LaurentFrx/camera-RPi5-comptage/hardware/camera-arm/renders/05_pose_plongee.png

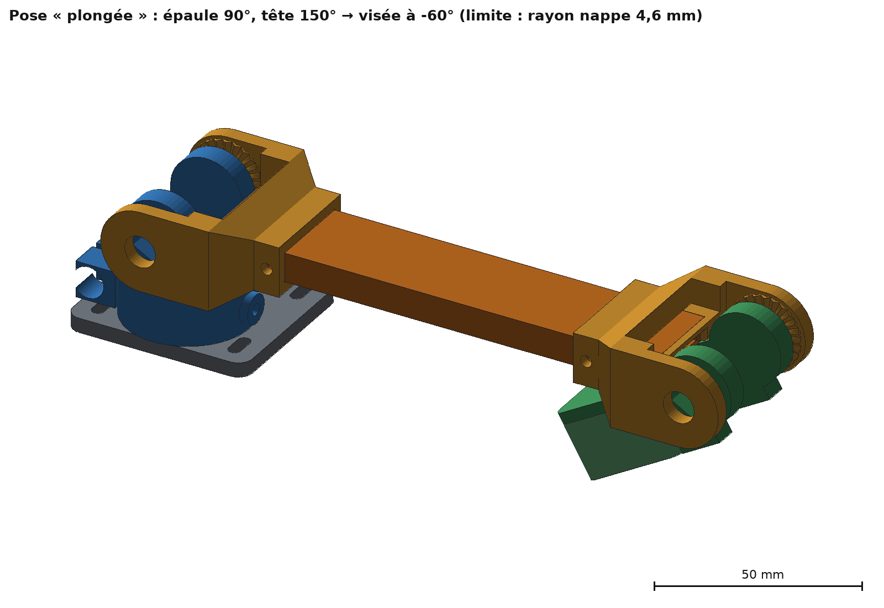
hardware/camera-arm/renders/05_pose_plongee.png
