LaurentFrx/camera-RPi5-comptage/hardware/camera-arm/renders/20_piece_01b_cavalier_adaptateur.png

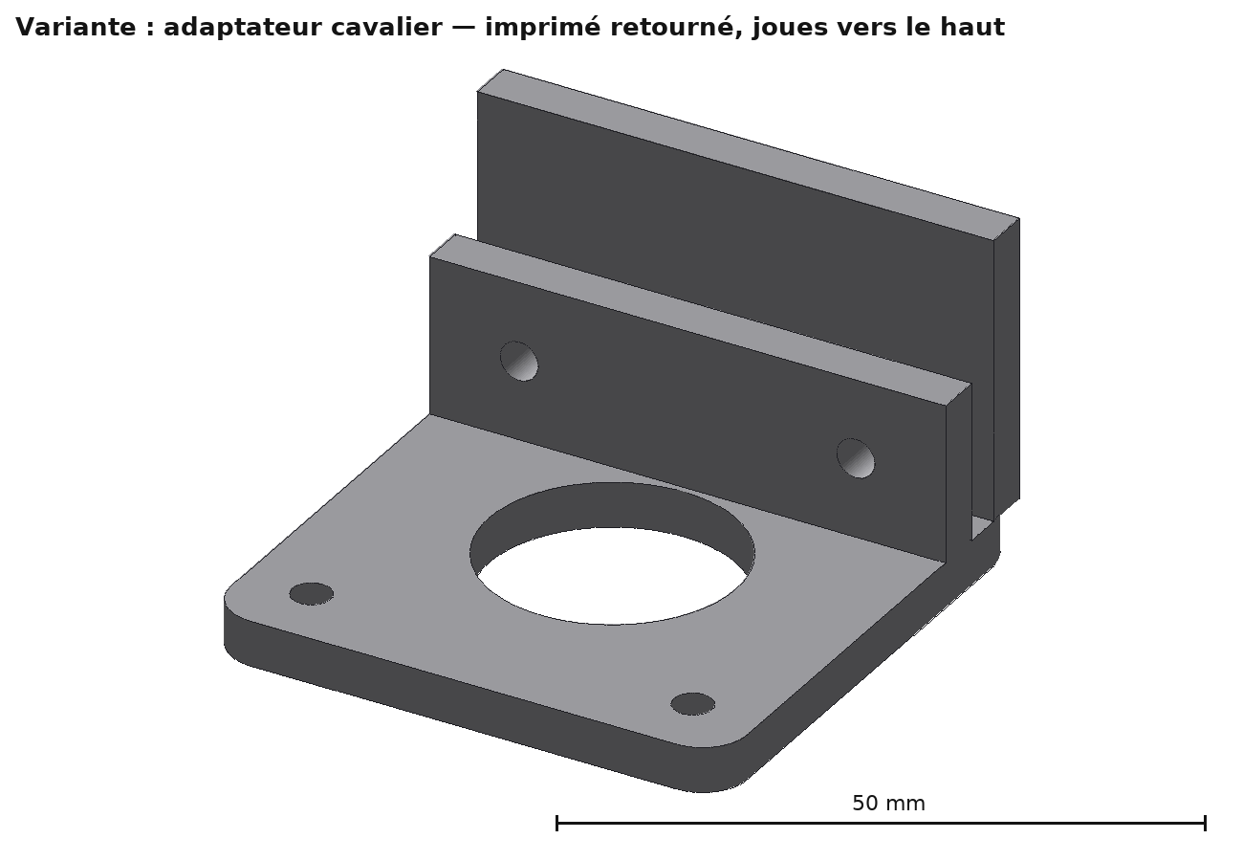
hardware/camera-arm/renders/20_piece_01b_cavalier_adaptateur.png
