LaurentFrx/camera-RPi5-comptage/hardware/camera-arm/renders/20_piece_01c_gabarit_percage_couvercle.png

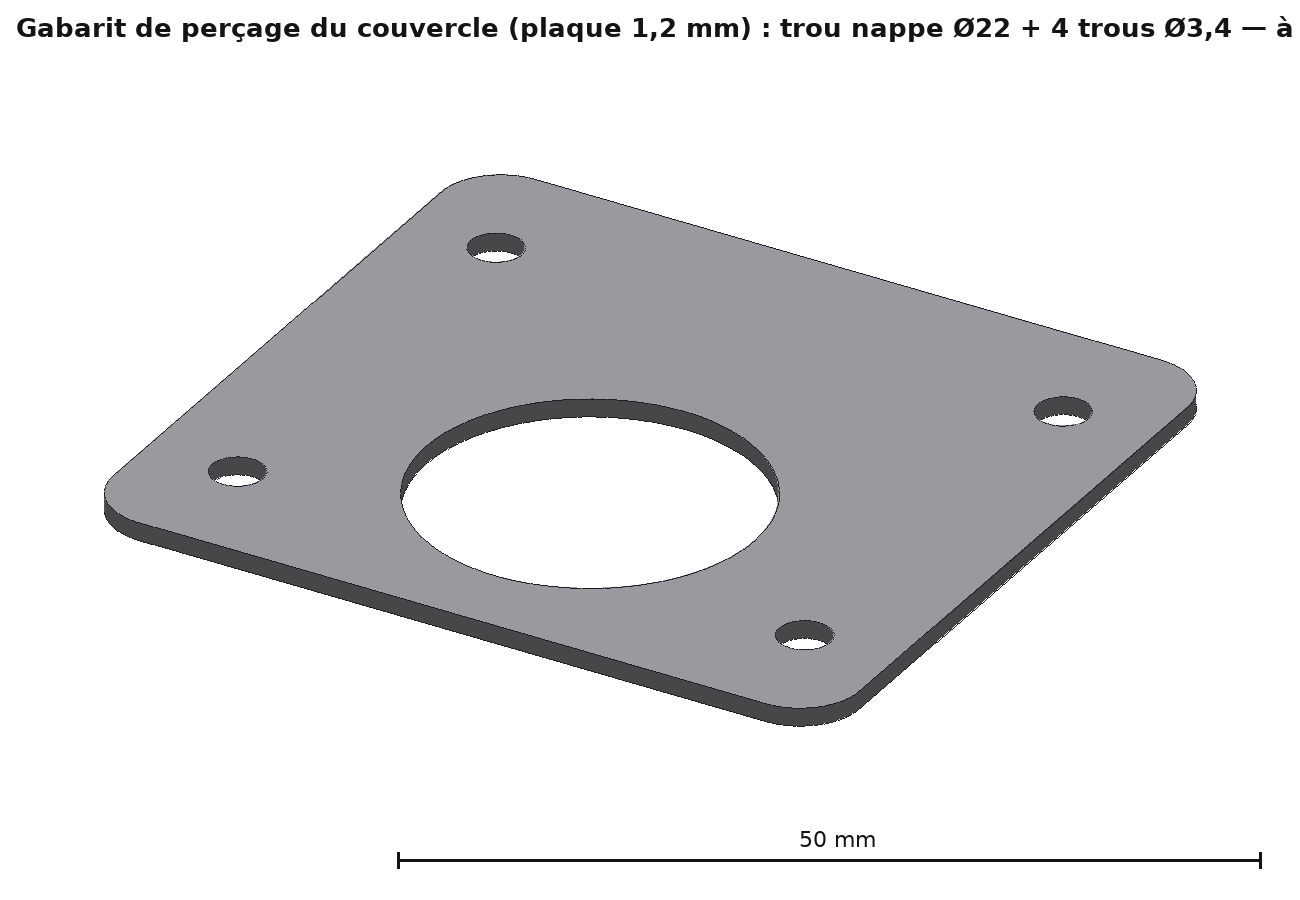
hardware/camera-arm/renders/20_piece_01c_gabarit_percage_couvercle.png
