LaurentFrx/camera-RPi5-comptage/hardware/camera-arm/renders/20_piece_04a_bras_corps_L150.png

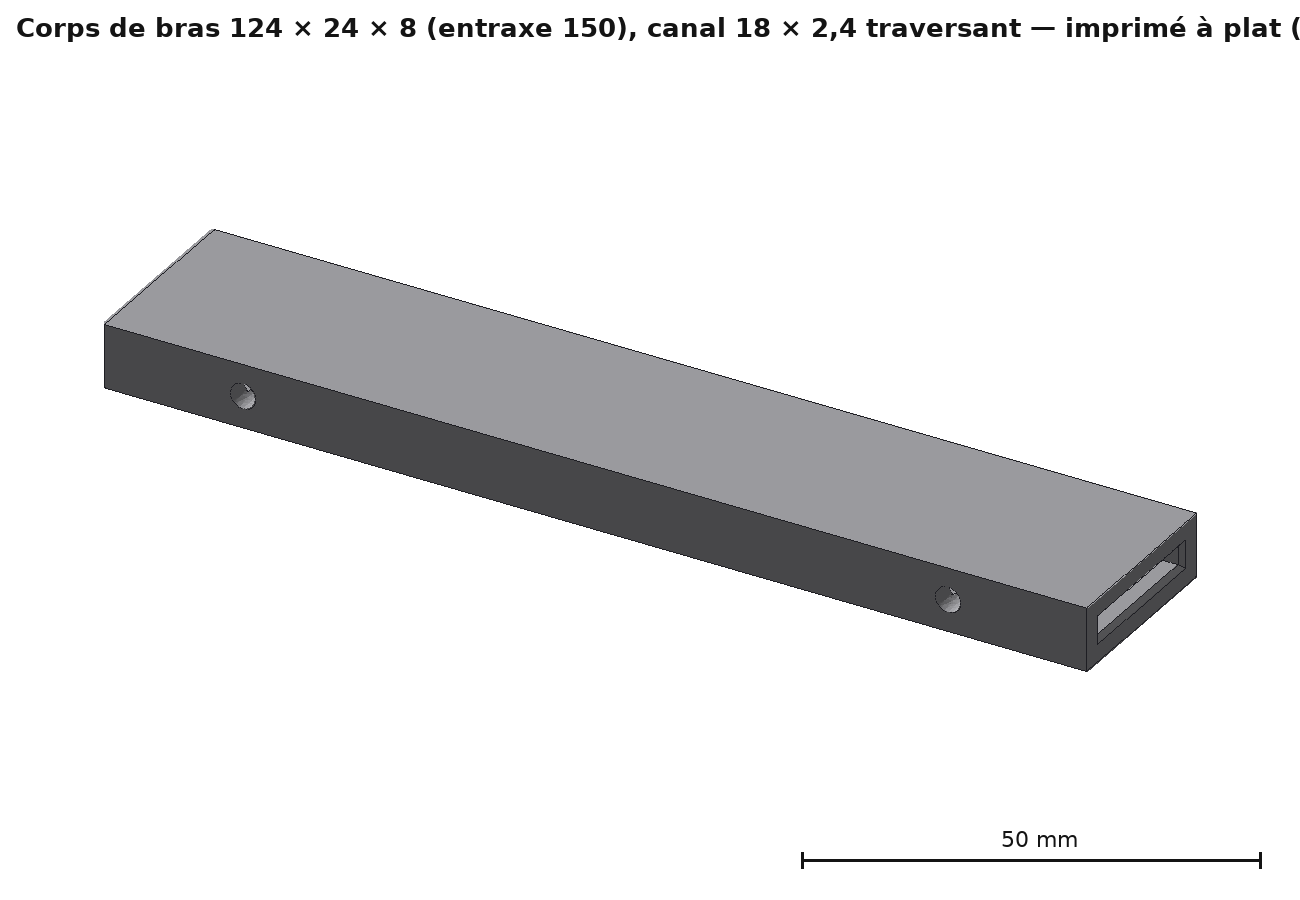
hardware/camera-arm/renders/20_piece_04a_bras_corps_L150.png
