LaurentFrx/camera-RPi5-comptage/hardware/camera-arm/renders/20_piece_04a_bras_corps_L170_alt.png

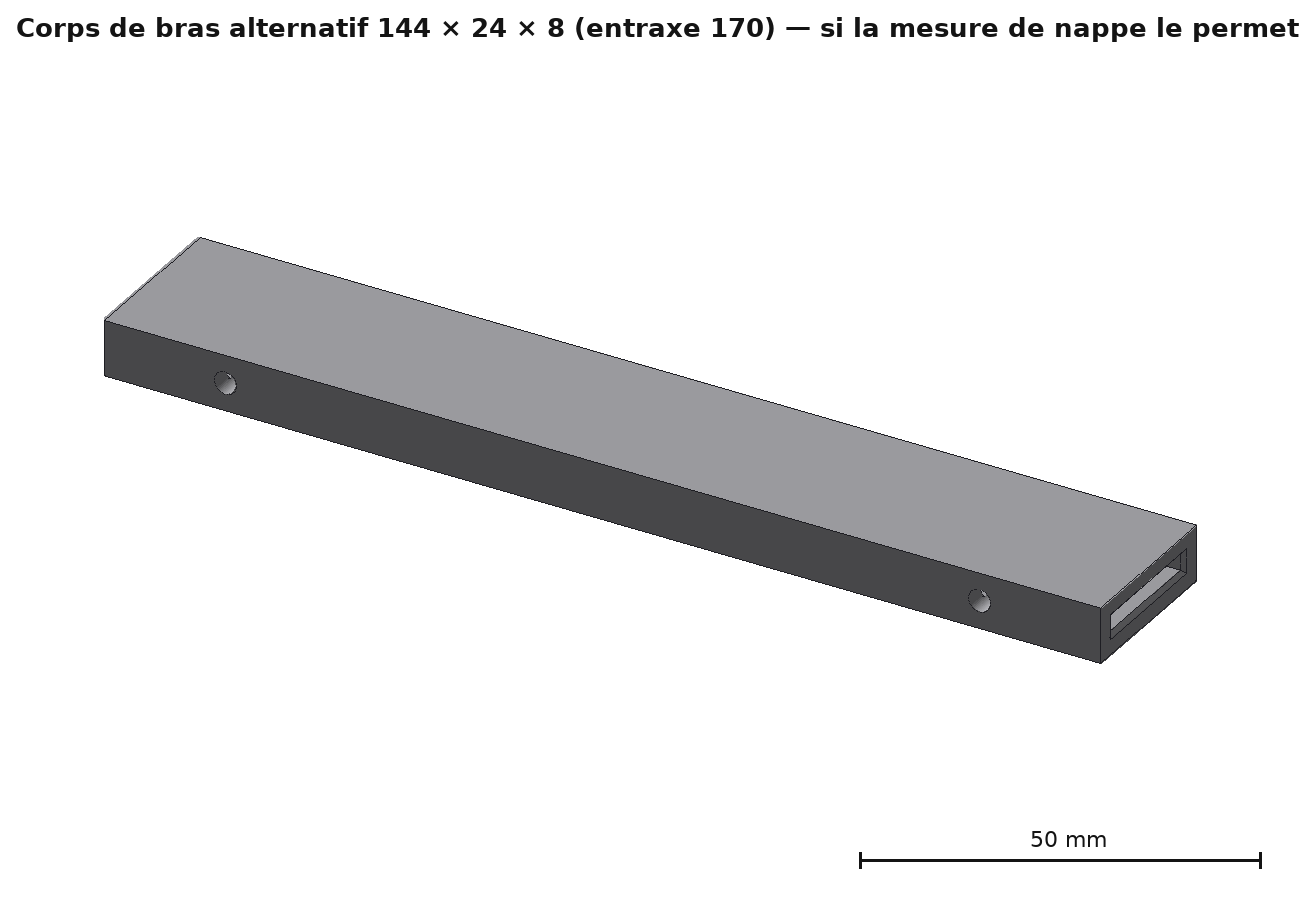
hardware/camera-arm/renders/20_piece_04a_bras_corps_L170_alt.png
