LaurentFrx/camera-RPi5-comptage/hardware/camera-arm/renders/20_piece_04c_goupille_x5.png

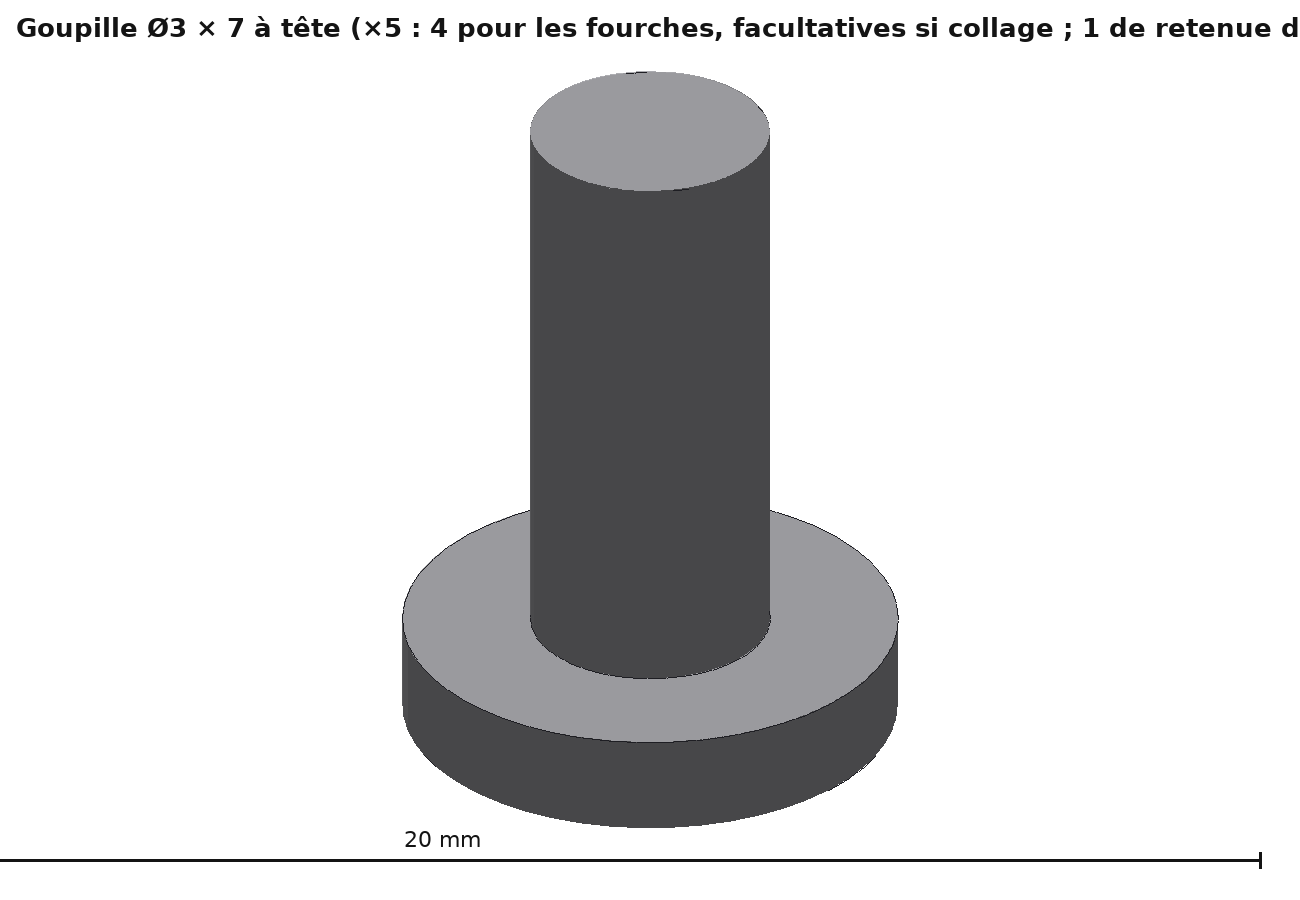
hardware/camera-arm/renders/20_piece_04c_goupille_x5.png
