LaurentFrx/camera-RPi5-comptage/hardware/camera-arm/renders/20_piece_06_tete_facade.png

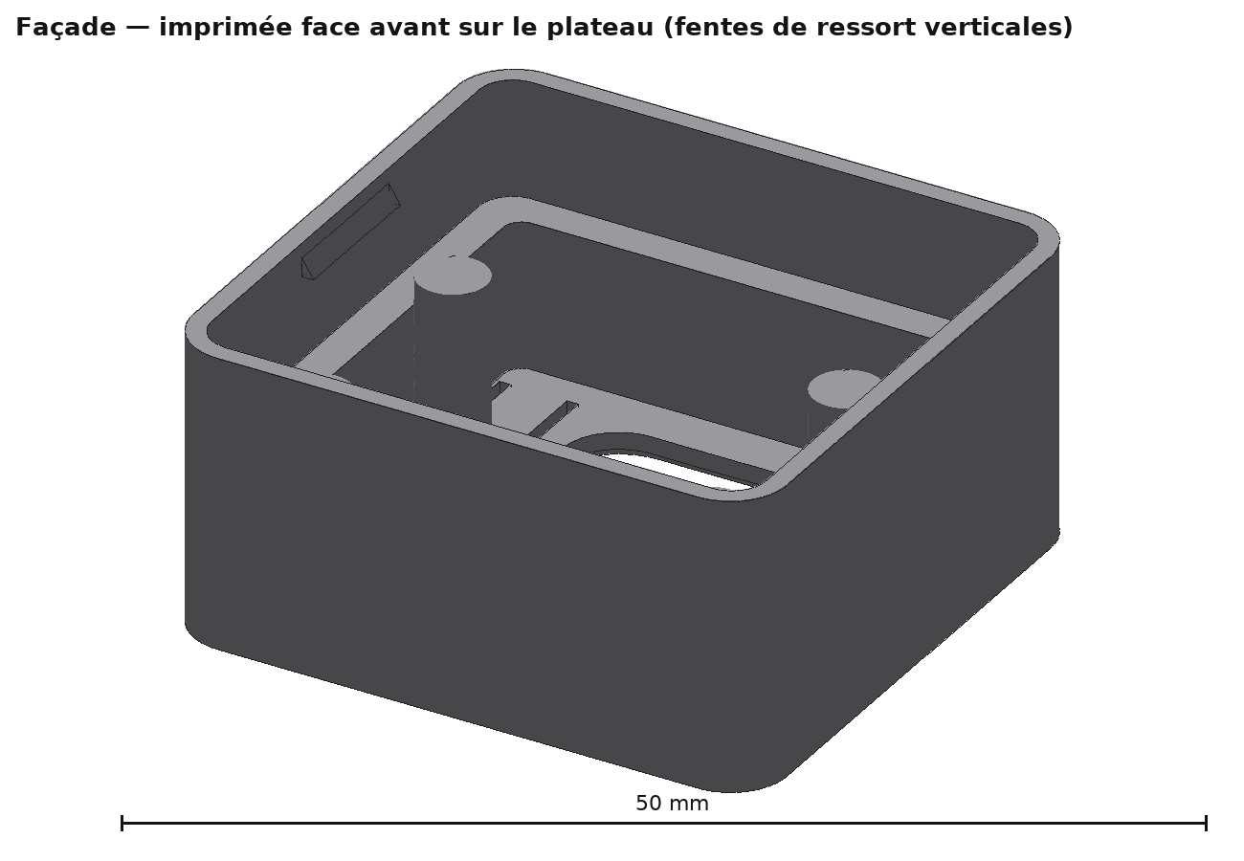
hardware/camera-arm/renders/20_piece_06_tete_facade.png
