LaurentFrx/camera-RPi5-comptage/hardware/camera-arm/renders/20_piece_07_vis_M8_L11_x4.png

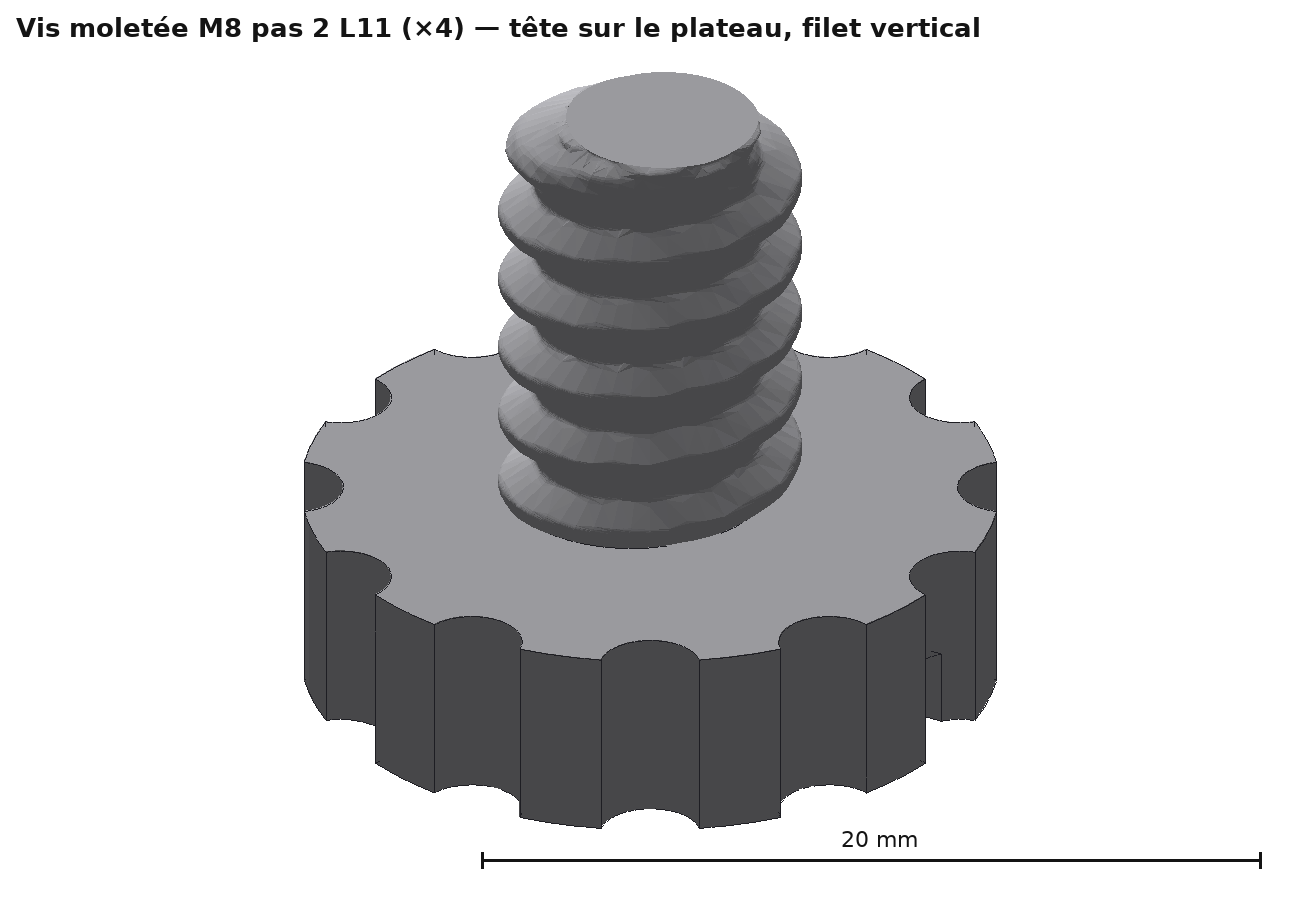
hardware/camera-arm/renders/20_piece_07_vis_M8_L11_x4.png
