LaurentFrx/camera-RPi5-comptage/hardware/camera-arm/renders/20_piece_09_ecrou_rosette_x4.png

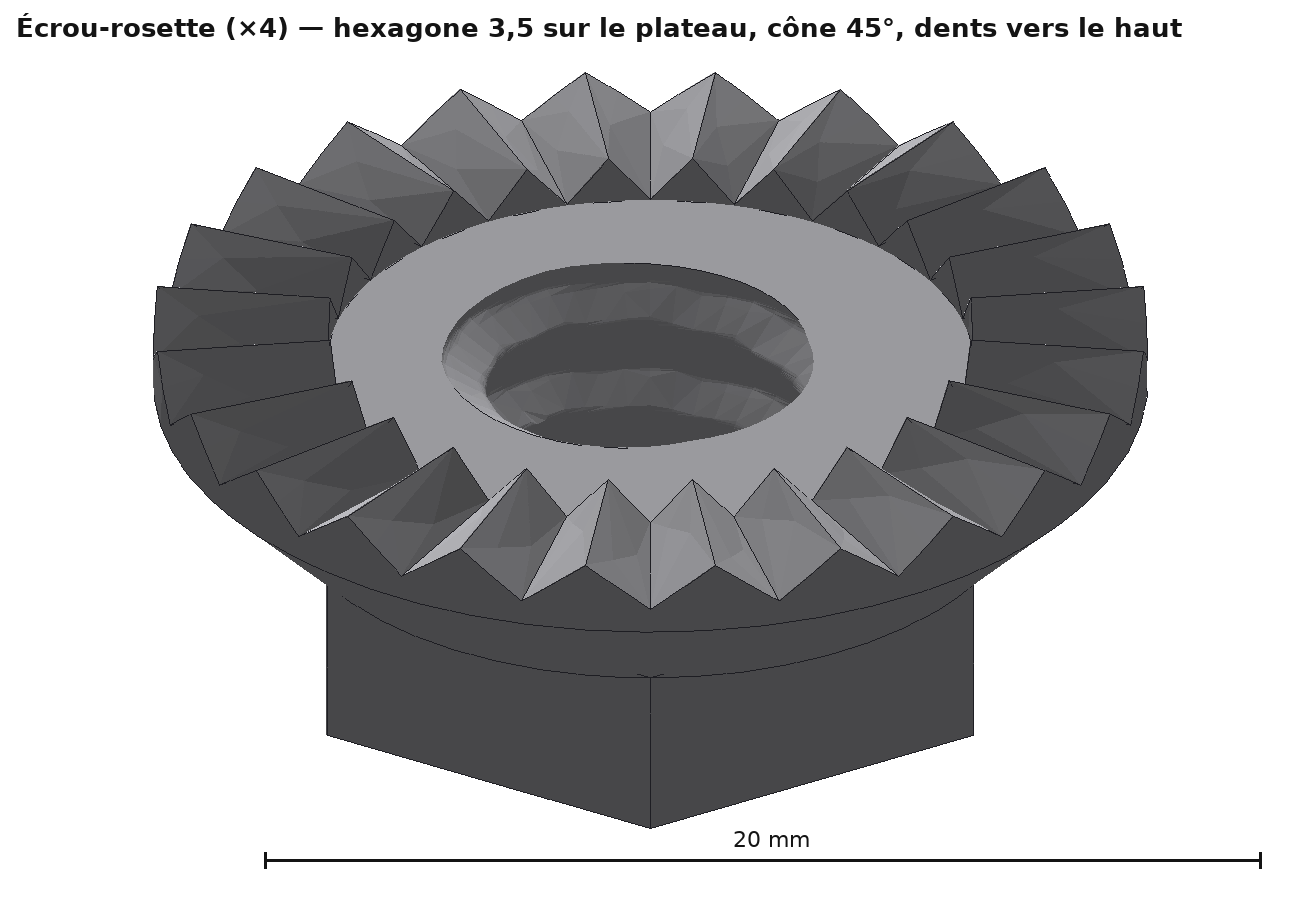
hardware/camera-arm/renders/20_piece_09_ecrou_rosette_x4.png
