LaurentFrx/camera-RPi5-comptage/hardware/camera-arm/renders/20_piece_10_ecrou_hex.png

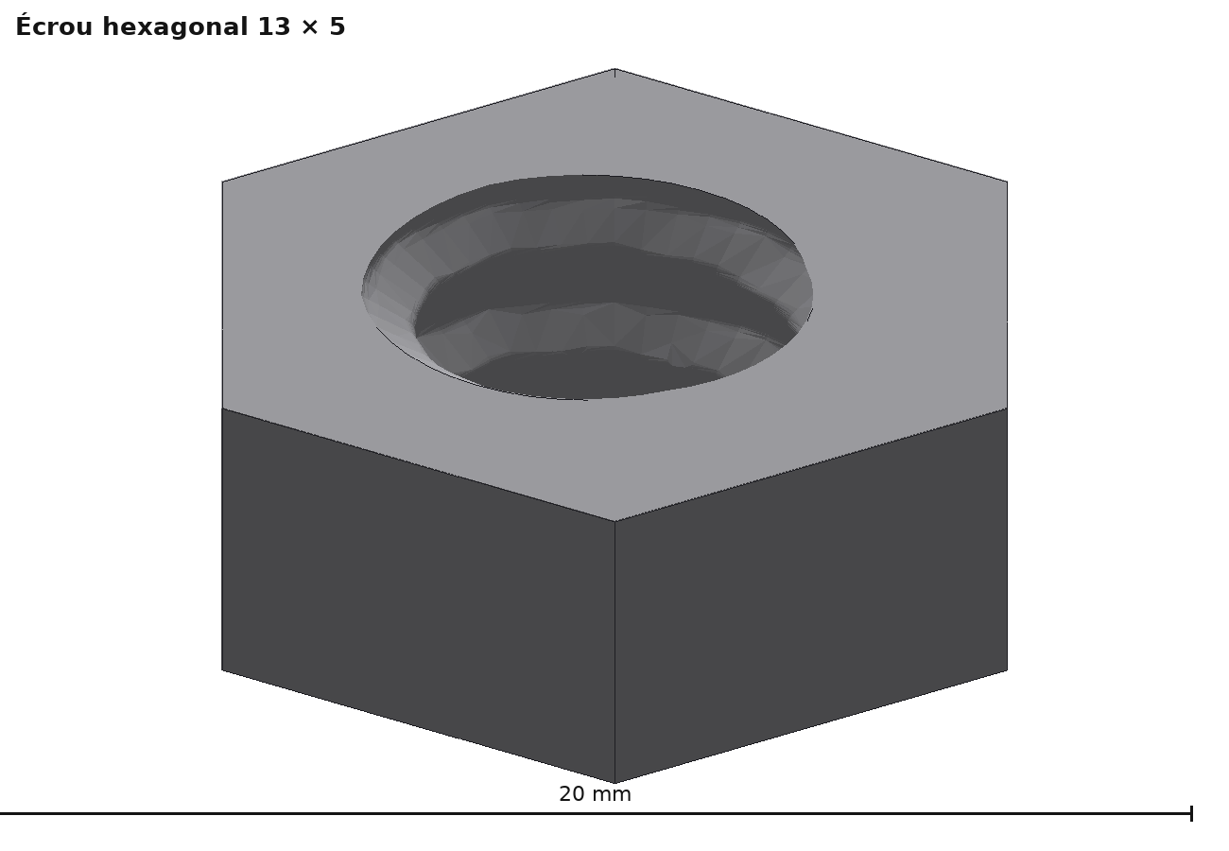
hardware/camera-arm/renders/20_piece_10_ecrou_hex.png
