LaurentFrx/camera-RPi5-comptage/hardware/camera-arm/export/step/10_ecrou_hex.step

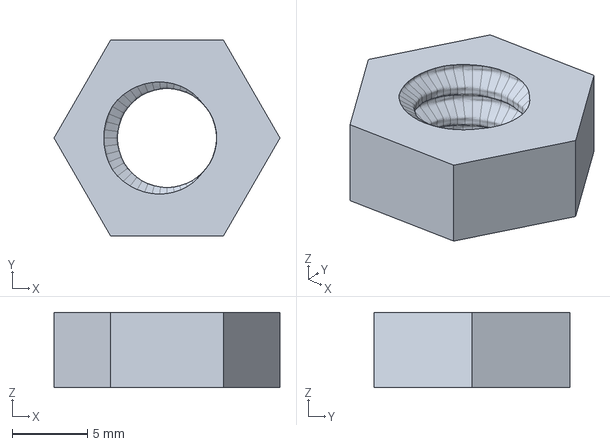
[picture p47: CAD file, 2026-10-01]
hardware/camera-arm/export/step/10_ecrou_hex.step
15.0 x 13.0 x 5.00 mm
