LaurentFrx/camera-RPi5-comptage/hardware/camera-arm/export/step/04a_bras_corps_L170_alt.step

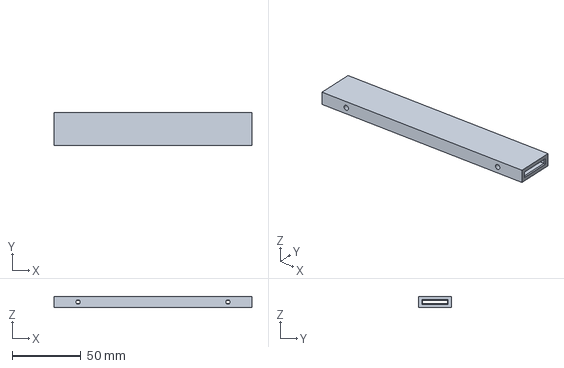
[picture p48: CAD file, 2026-10-01]
hardware/camera-arm/export/step/04a_bras_corps_L170_alt.step
144.0 x 24.0 x 8.00 mm
