LaurentFrx/camera-RPi5-comptage/hardware/camera-arm/export/step/04c_goupille_x5.step

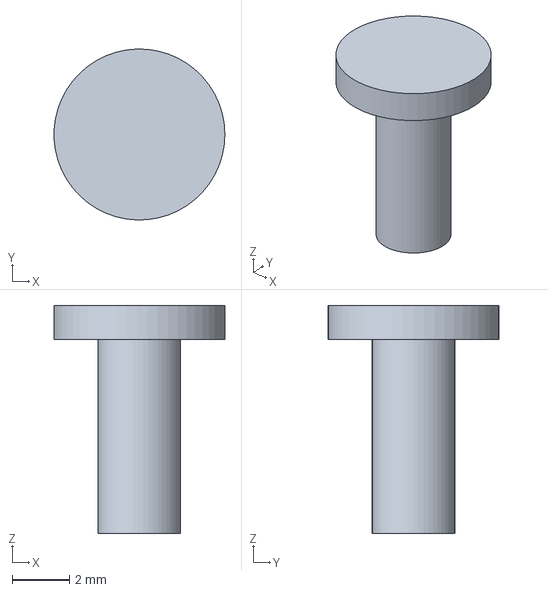
[picture p49: CAD file, 2026-10-01]
hardware/camera-arm/export/step/04c_goupille_x5.step
5.99 x 6.00 x 8.00 mm
