LaurentFrx/camera-RPi5-comptage/hardware/camera-arm/export/step/90_maquette_cm3.step

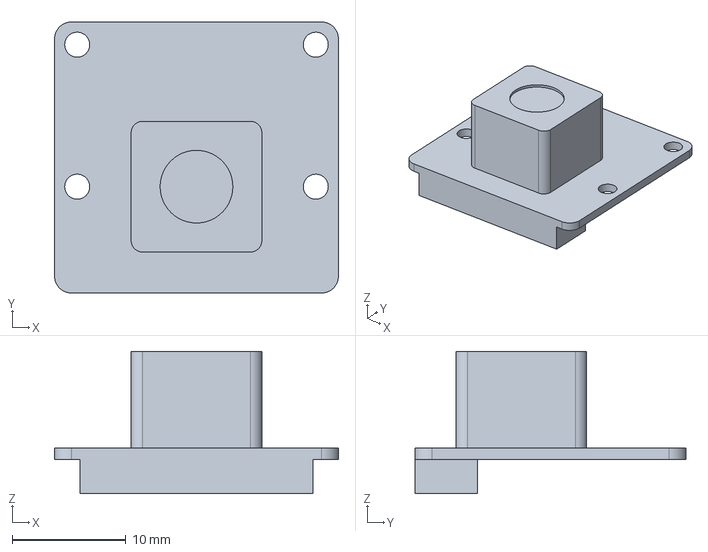
[picture p50: CAD file, 2026-10-01]
hardware/camera-arm/export/step/90_maquette_cm3.step
25.0 x 23.9 x 12.5 mm
