LaurentFrx/camera-RPi5-comptage/hardware/camera-arm/export/step/04b_fourche_x2.step

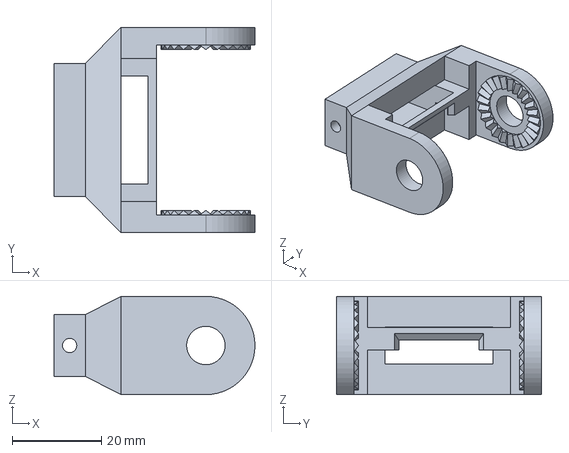
[picture p51: CAD file, 2026-10-01]
hardware/camera-arm/export/step/04b_fourche_x2.step
45.0 x 46.0 x 22.0 mm
