LaurentFrx/camera-RPi5-comptage/hardware/camera-arm/renders/03_assemblage_dessus.png

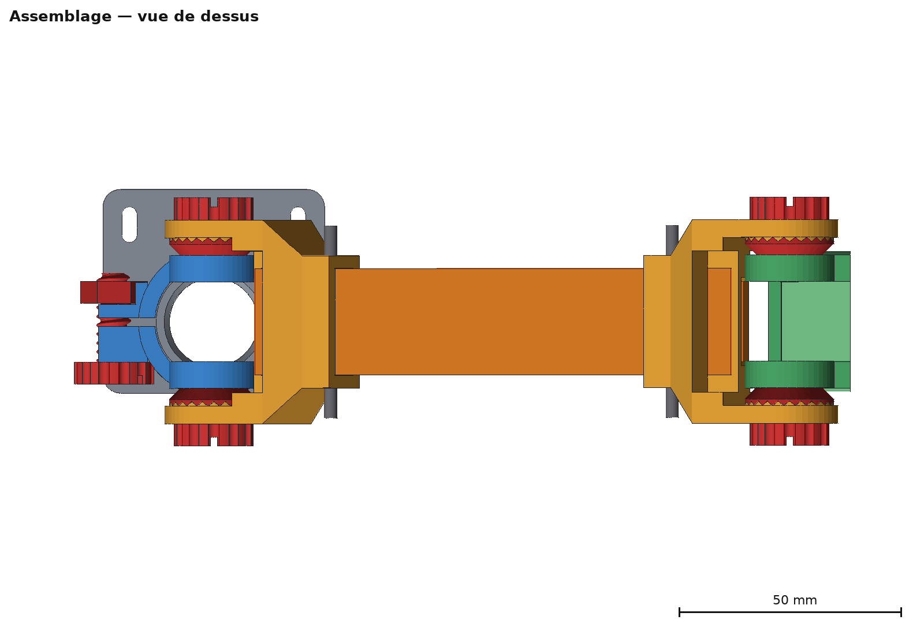
hardware/camera-arm/renders/03_assemblage_dessus.png
