LaurentFrx/camera-RPi5-comptage/hardware/camera-arm/renders/04_assemblage_cote.png

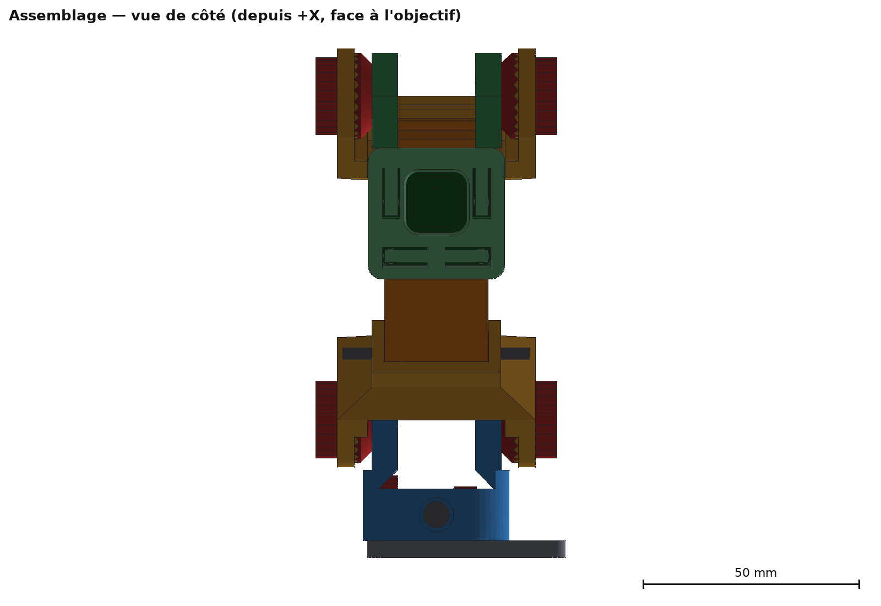
hardware/camera-arm/renders/04_assemblage_cote.png
